D4VI365/HotWheelClock/CAD/InnerCurb1.stl

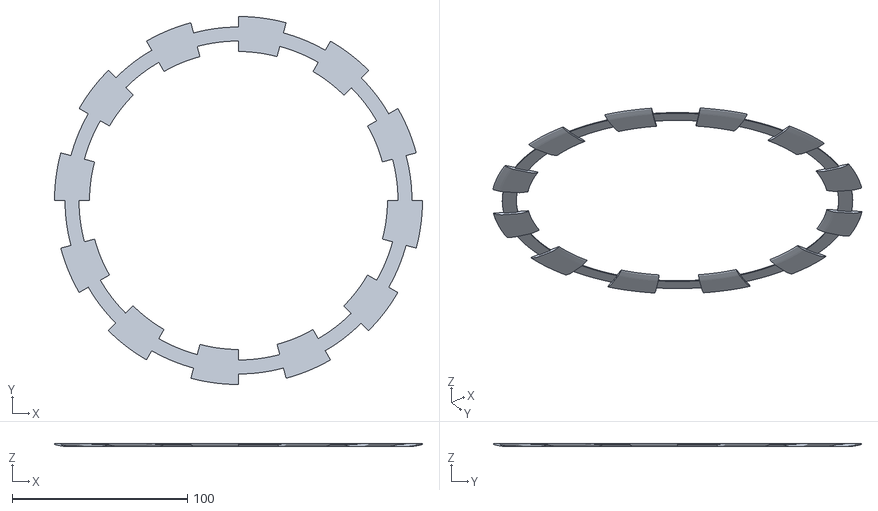
[picture p19: CAD file, 2026-04-08]
CAD/InnerCurb1.stl
210.0 x 210.0 x 1.51
