D4VI365/HotWheelClock/CAD/OuterCurb3.stl

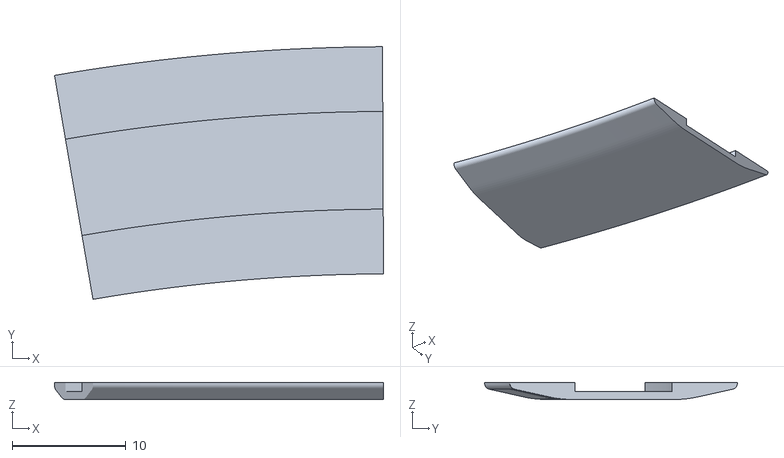
[picture p20: CAD file, 2026-04-08]
CAD/OuterCurb3.stl
29.0 x 22.2 x 1.50
