D4VI365/HotWheelClock/CAD/OuterCurb1.stl

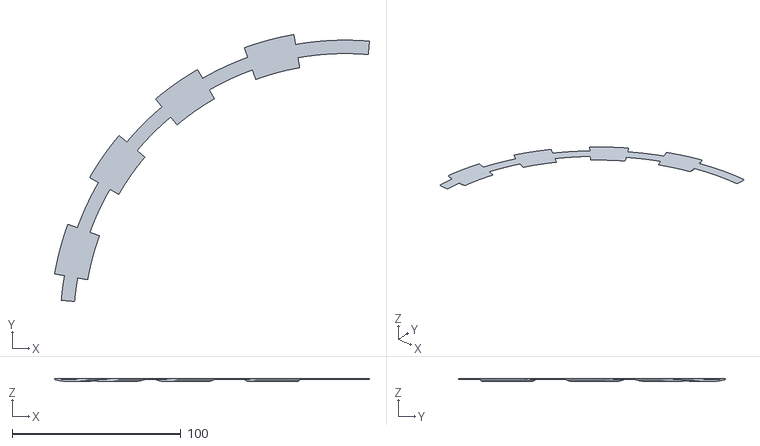
[picture p21: CAD file, 2026-04-08]
CAD/OuterCurb1.stl
186.8 x 158.3 x 1.51
