D4VI365/HotWheelClock/CAD/OuterHook.stl

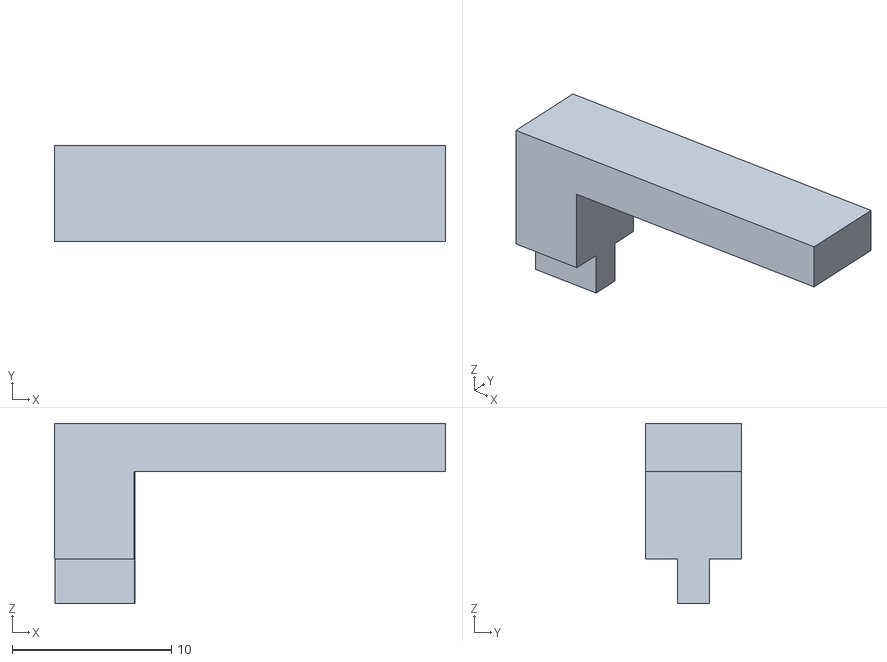
[picture p22: CAD file, 2026-04-08]
CAD/OuterHook.stl
24.5 x 6.00 x 11.3
