D4VI365/HotWheelClock/CAD/InnerHookHall.stl

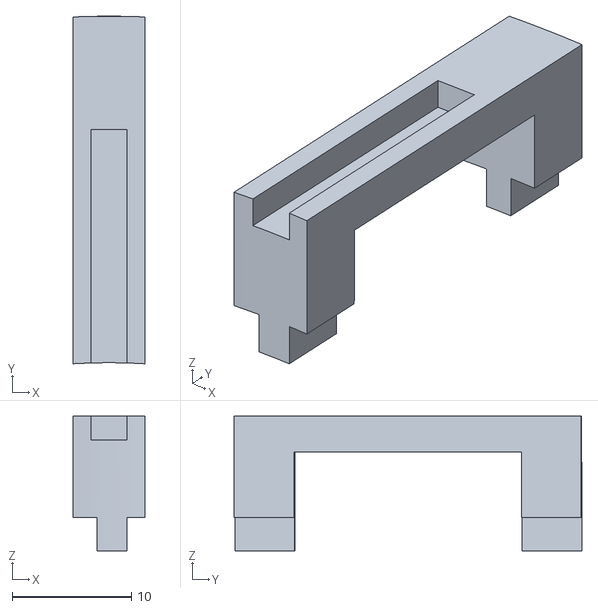
[picture p23: CAD file, 2026-04-08]
CAD/InnerHookHall.stl
6.00 x 29.1 x 11.3
