D4VI365/HotWheelClock/CAD/InnerCurb2.stl

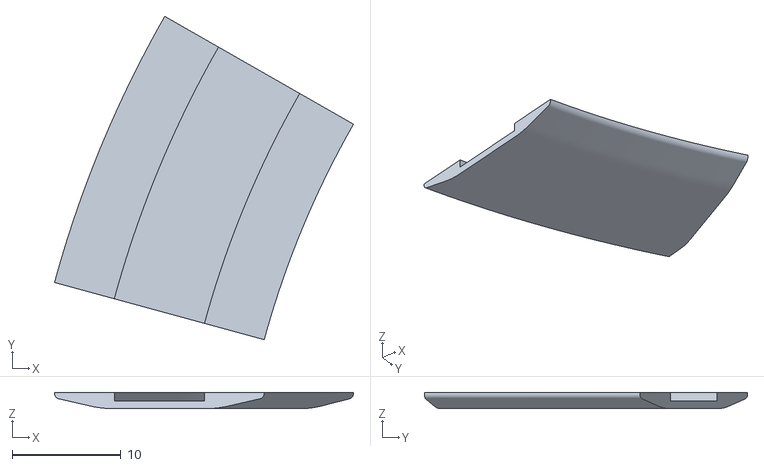
[picture p24: CAD file, 2026-04-08]
CAD/InnerCurb2.stl
27.5 x 29.7 x 1.50
