D4VI365/HotWheelClock/CAD/InnerMotorMount.stl

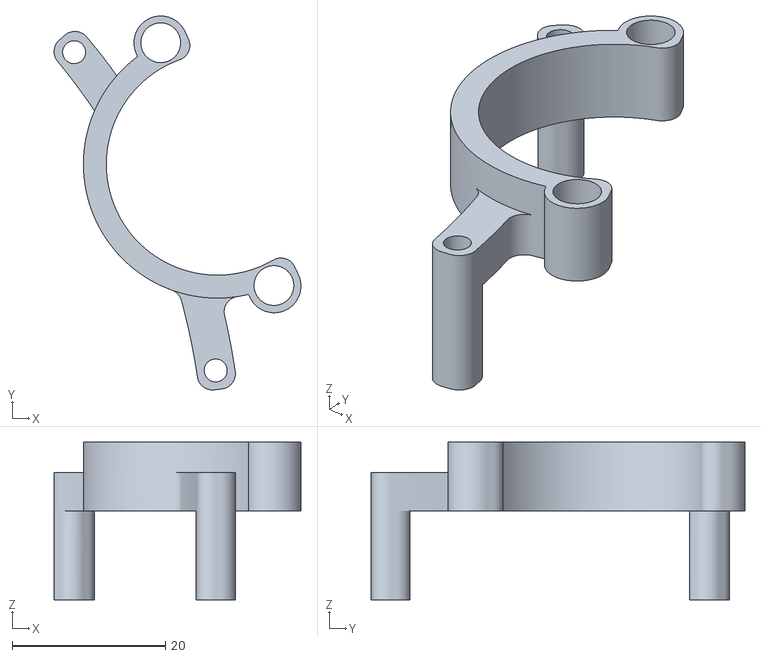
[picture p25: CAD file, 2026-04-08]
CAD/InnerMotorMount.stl
32.3 x 48.9 x 20.6
